danielbloy/pico-interactive-halloween/3d_models/fire/4xAA Battery Holder.png

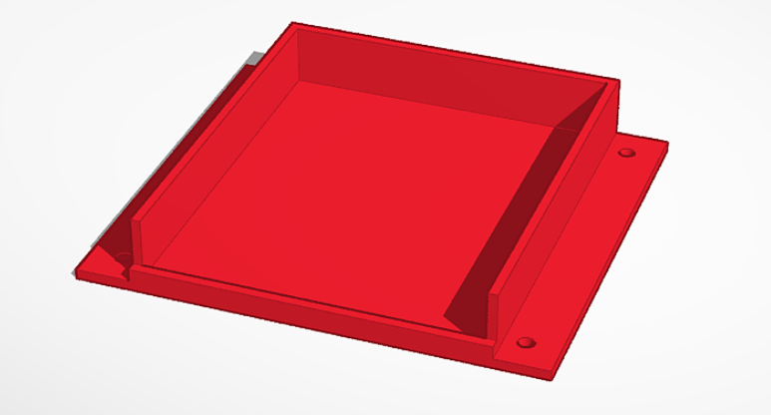
3d_models/fire/4xAA Battery Holder.png
