danielbloy/pico-interactive-halloween/3d_models/fire/Cable clip.png

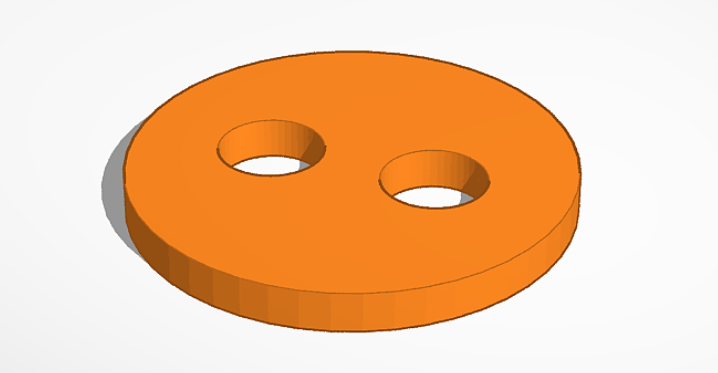
3d_models/fire/Cable clip.png
