danielbloy/pico-interactive-halloween/3d_models/fire/Circuit Board Holder.png

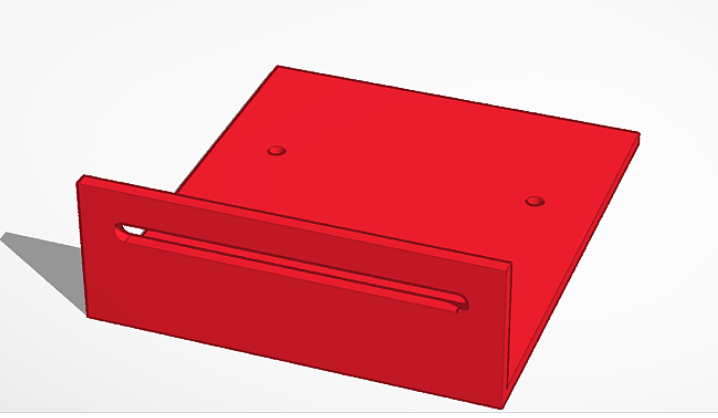
3d_models/fire/Circuit Board Holder.png
