danielbloy/pico-interactive-halloween/3d_models/fire/Eigth turn with holes.png

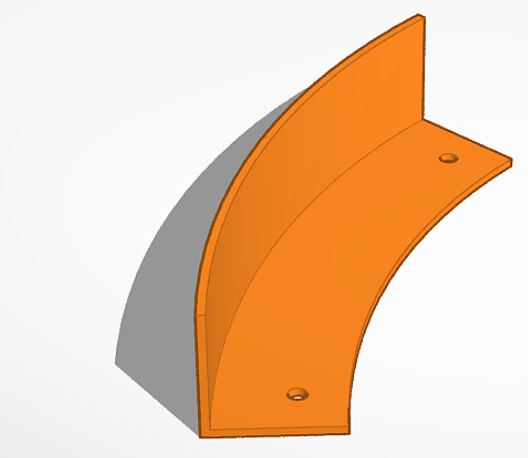
3d_models/fire/Eigth turn with holes.png
