danielbloy/pico-interactive-halloween/3d_models/fire/Eigth turn.png

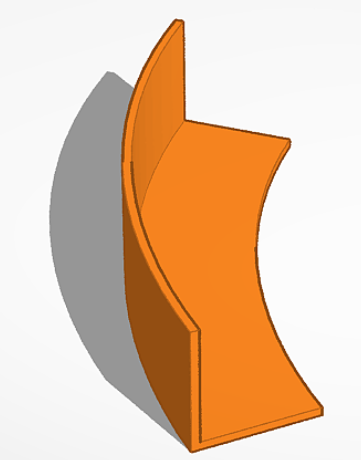
3d_models/fire/Eigth turn.png
