danielbloy/pico-interactive-halloween/3d_models/fire/Quater turn.png

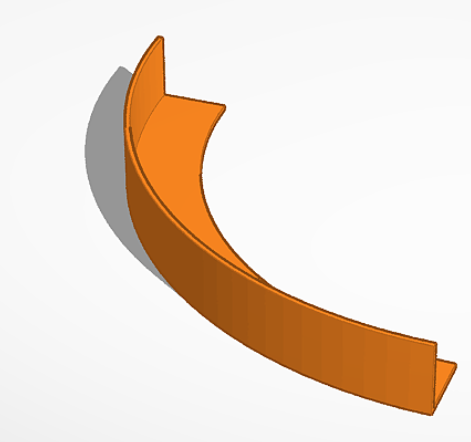
3d_models/fire/Quater turn.png
