danielbloy/pico-interactive-halloween/3d_models/speaker/Speaker Box Cover.stl

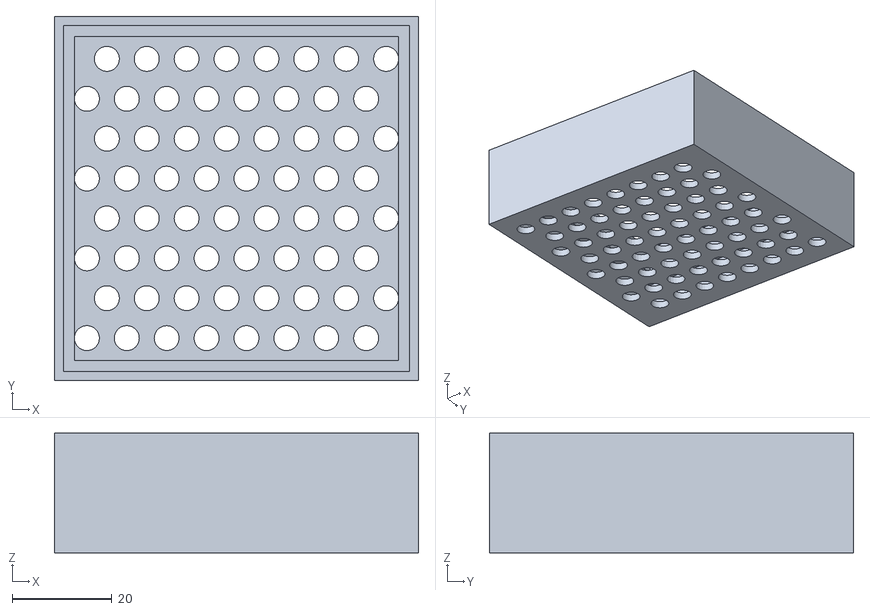
[picture p44: CAD file, 2024-10-30]
3d_models/speaker/Speaker Box Cover.stl
73.0 x 73.0 x 24.0
