danielbloy/pico-interactive-halloween/3d_models/spiders/Holder Mk 2.stl

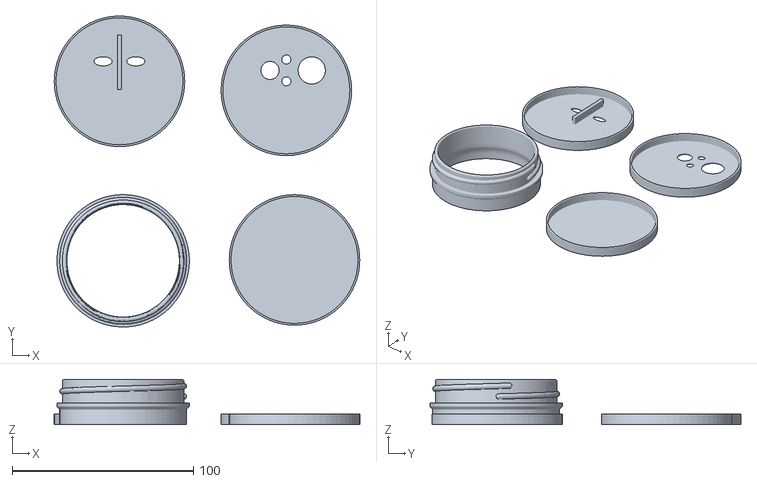
[picture p45: CAD file, 2024-10-30]
3d_models/spiders/Holder Mk 2.stl
168.5 x 171.5 x 25.0
