danielbloy/pico-interactive-halloween/3d_models/ultrasonic/Small Ultrasonic Clip.stl

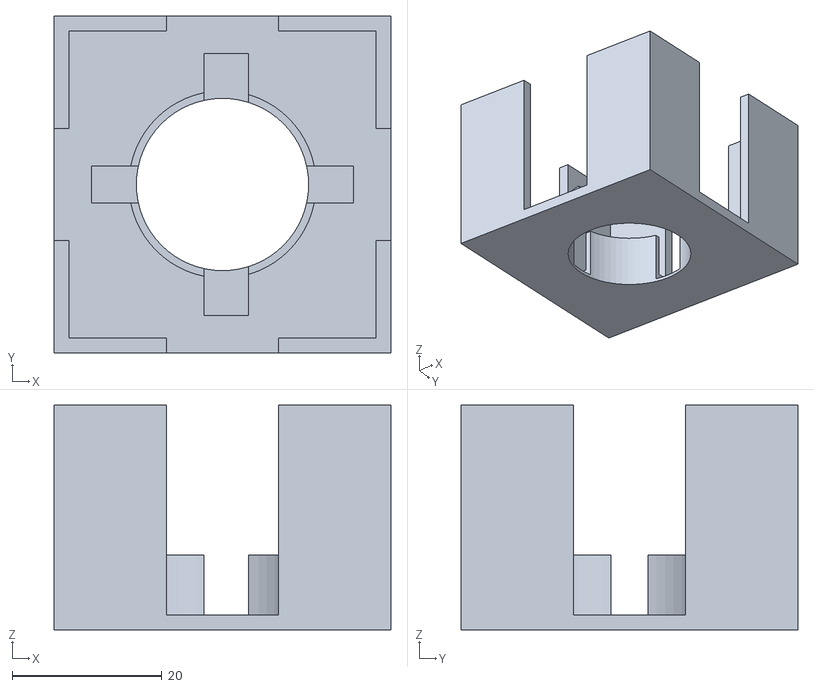
[picture p46: CAD file, 2024-10-30]
3d_models/ultrasonic/Small Ultrasonic Clip.stl
45.0 x 45.0 x 30.0
