danielbloy/pico-interactive-halloween/3d_models/fire/4xAA Battery Holder.stl

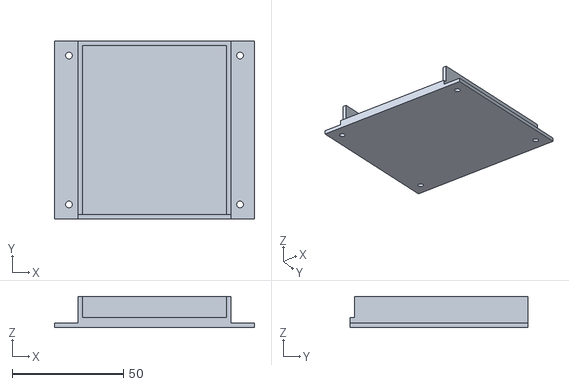
[picture p47: CAD file, 2025-09-02]
3d_models/fire/4xAA Battery Holder.stl
90.0 x 80.0 x 14.0
