danielbloy/pico-interactive-halloween/3d_models/skull_jar/Mason_jar_12mm_hole.stl

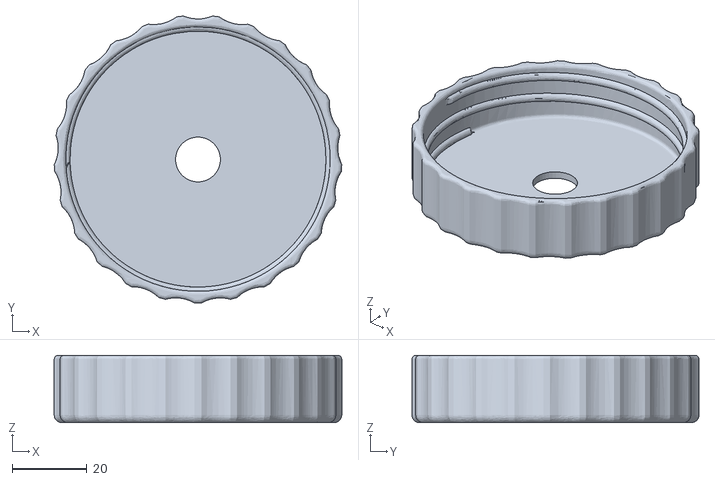
[picture p48: CAD file, 2024-10-30]
3d_models/skull_jar/Mason_jar_12mm_hole.stl
76.9 x 76.8 x 18.0
