danielbloy/pico-interactive-halloween/3d_models/spiders/Spider Pattern.stl

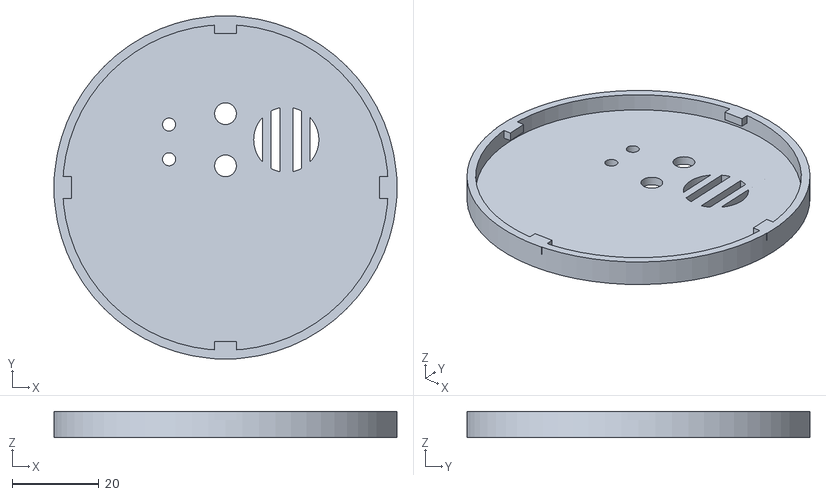
[picture p49: CAD file, 2024-10-30]
3d_models/spiders/Spider Pattern.stl
79.0 x 79.0 x 6.00
