danielbloy/pico-interactive-halloween/3d_models/ultrasonic/Ultrasonic Clip.stl

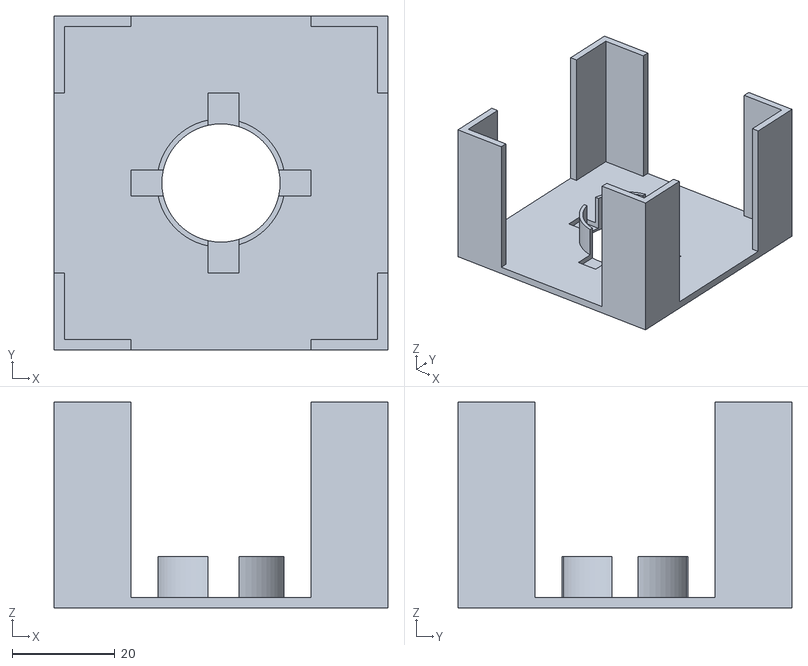
[picture p50: CAD file, 2024-10-30]
3d_models/ultrasonic/Ultrasonic Clip.stl
65.0 x 65.0 x 40.0
