danielbloy/pico-interactive-halloween/3d_models/fire/Cable clip.stl

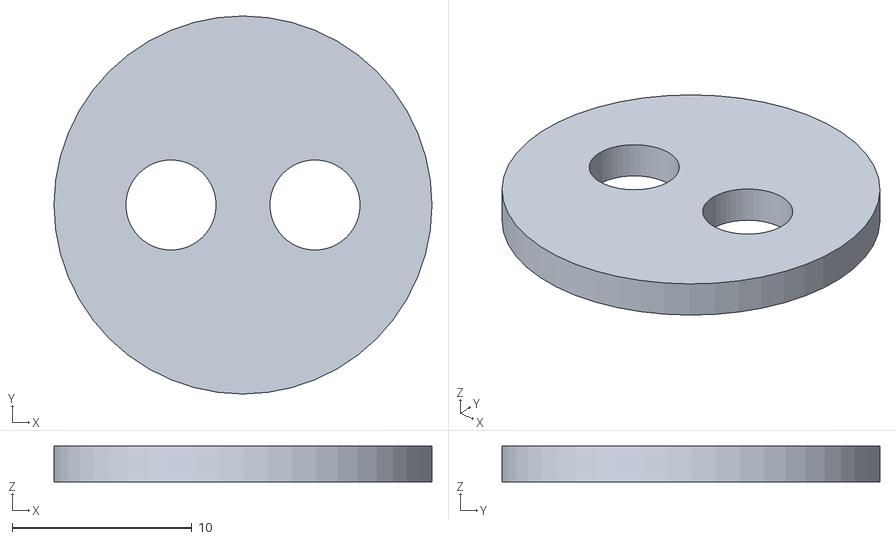
[picture p51: CAD file, 2025-09-02]
3d_models/fire/Cable clip.stl
21.0 x 21.0 x 2.00
