danielbloy/pico-interactive-halloween/3d_models/skull_jar/Neopixel_ring_holder_52mm_base.stl

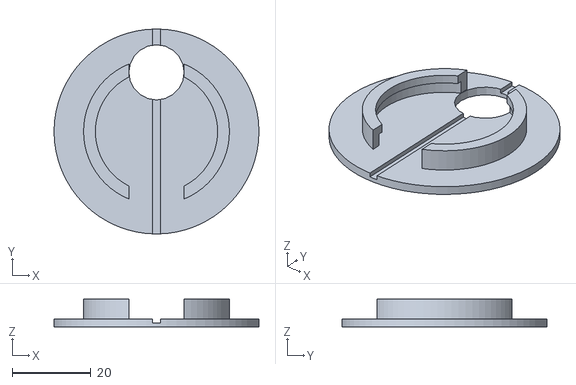
[picture p52: CAD file, 2024-10-30]
3d_models/skull_jar/Neopixel_ring_holder_52mm_base.stl
52.0 x 52.0 x 7.00
