danielbloy/pico-interactive-halloween/3d_models/spiders/Holder.stl

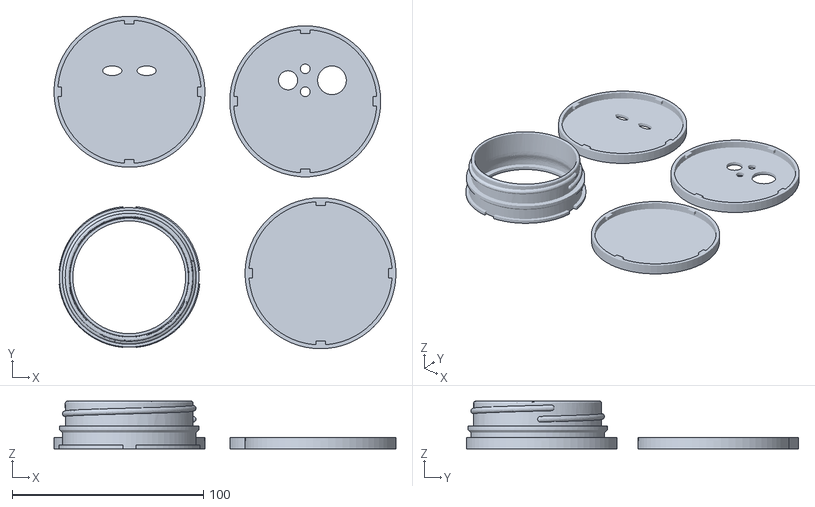
[picture p53: CAD file, 2024-10-30]
3d_models/spiders/Holder.stl
179.0 x 174.0 x 25.0
