danielbloy/pico-interactive-halloween/3d_models/ultrasonic/Ultrasonic Box Plugs.stl

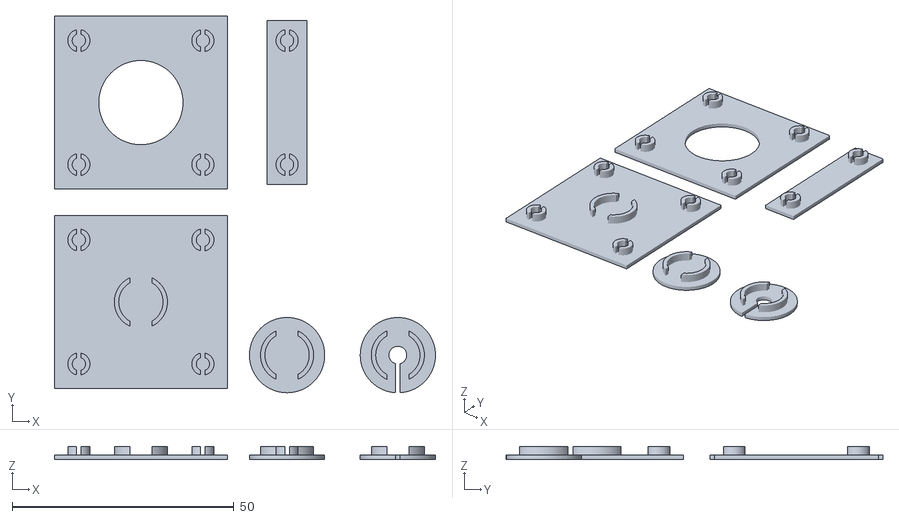
[picture p54: CAD file, 2024-10-30]
3d_models/ultrasonic/Ultrasonic Box Plugs.stl
86.0 x 85.0 x 3.00
