danielbloy/pico-interactive-halloween/3d_models/fire/Circuit Board Holder.stl

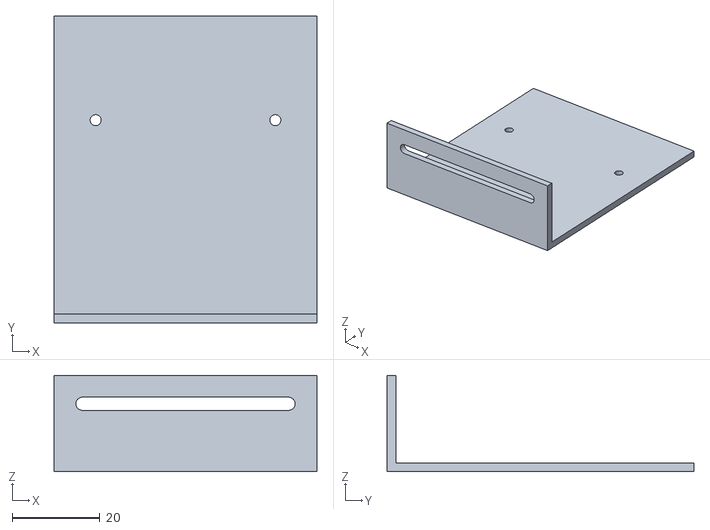
[picture p55: CAD file, 2025-09-02]
3d_models/fire/Circuit Board Holder.stl
60.0 x 70.0 x 22.0
