danielbloy/pico-interactive-halloween/3d_models/skull_jar/Neopixel_ring_holder_57mm_clip.stl

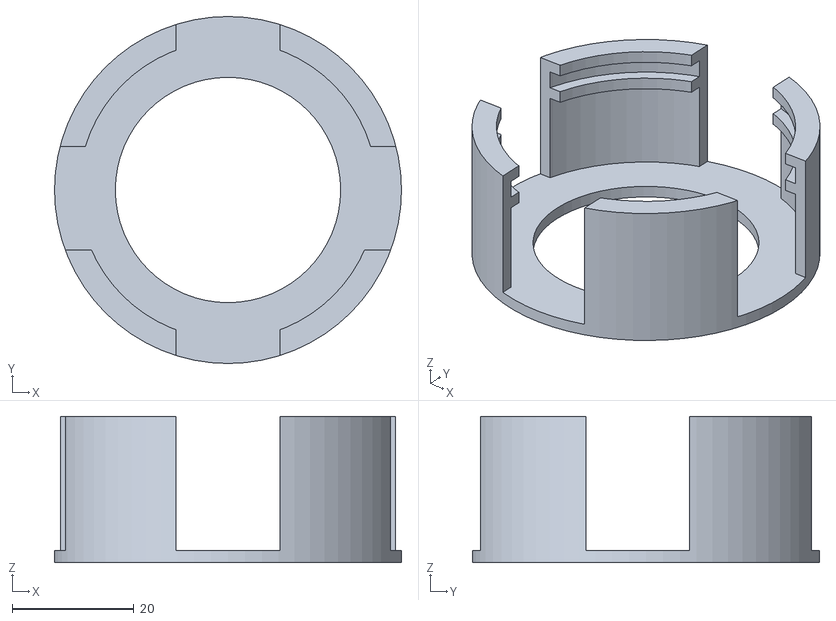
[picture p56: CAD file, 2024-10-30]
3d_models/skull_jar/Neopixel_ring_holder_57mm_clip.stl
57.0 x 57.0 x 24.0
