danielbloy/pico-interactive-halloween/3d_models/ultrasonic/Ultrasonic Box.stl

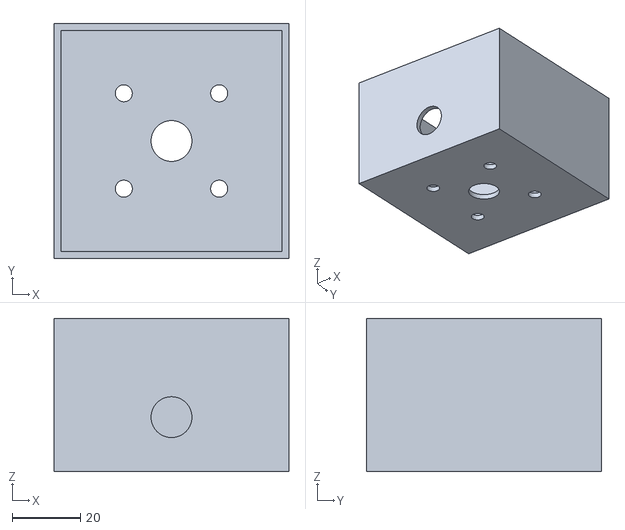
[picture p57: CAD file, 2024-10-30]
3d_models/ultrasonic/Ultrasonic Box.stl
69.0 x 69.0 x 45.0
