danielbloy/pico-interactive-halloween/3d_models/fire/Quater turn.stl

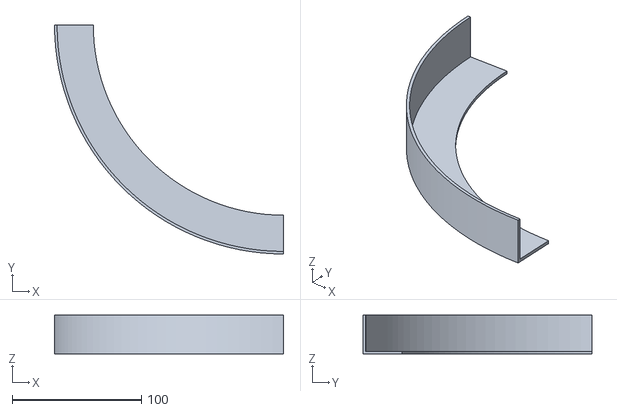
[picture p58: CAD file, 2025-09-02]
3d_models/fire/Quater turn.stl
177.0 x 177.0 x 30.0
