danielbloy/pico-interactive-halloween/3d_models/skull_jar/Mason_jar_id_with_57mm_clip.stl

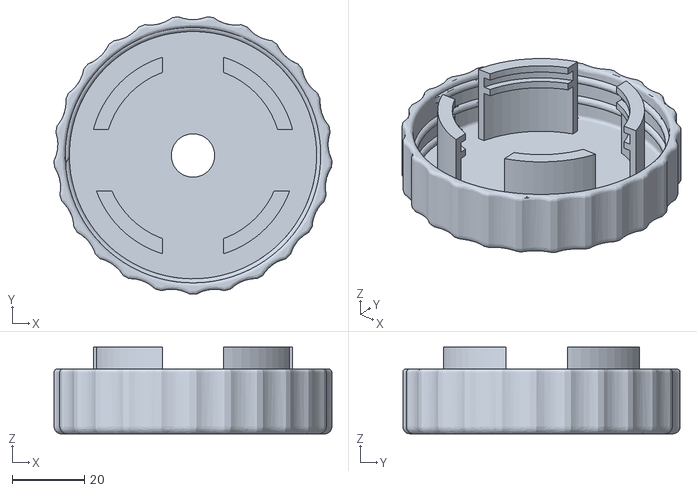
[picture p59: CAD file, 2024-10-30]
3d_models/skull_jar/Mason_jar_id_with_57mm_clip.stl
76.9 x 76.8 x 24.0
