danielbloy/pico-interactive-halloween/3d_models/skull_jar/Neopixel_ring_holder_52mm_base_tall.stl

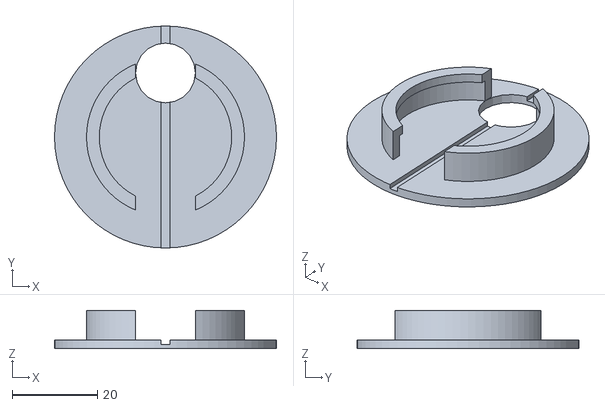
[picture p60: CAD file, 2024-10-30]
3d_models/skull_jar/Neopixel_ring_holder_52mm_base_tall.stl
52.0 x 52.0 x 9.00
