danielbloy/pico-interactive-halloween/microcontroller/makecode-arcade/eyes/arcade-eye-animation-blink-red-modified-ultrassonic.png

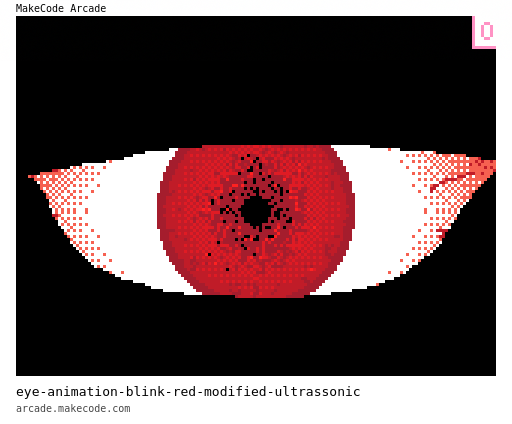
microcontroller/makecode-arcade/eyes/arcade-eye-animation-blink-red-modified-ultrassonic.png
