danielbloy/pico-interactive-halloween/microcontroller/makecode-arcade/eyes/constructing_new_eyes/1_original_creepy_head_box.jpg

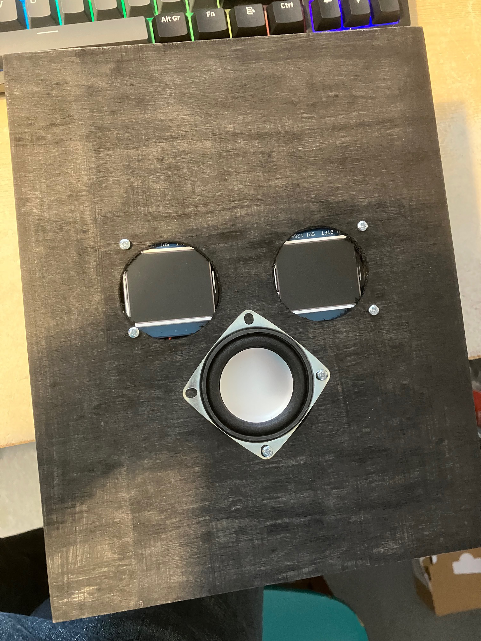
microcontroller/makecode-arcade/eyes/constructing_new_eyes/1_original_creepy_head_box.jpg
