danielbloy/pico-interactive-halloween/microcontroller/makecode-arcade/eyes/constructing_new_eyes/1b_original_creepy_head_inside.jpg

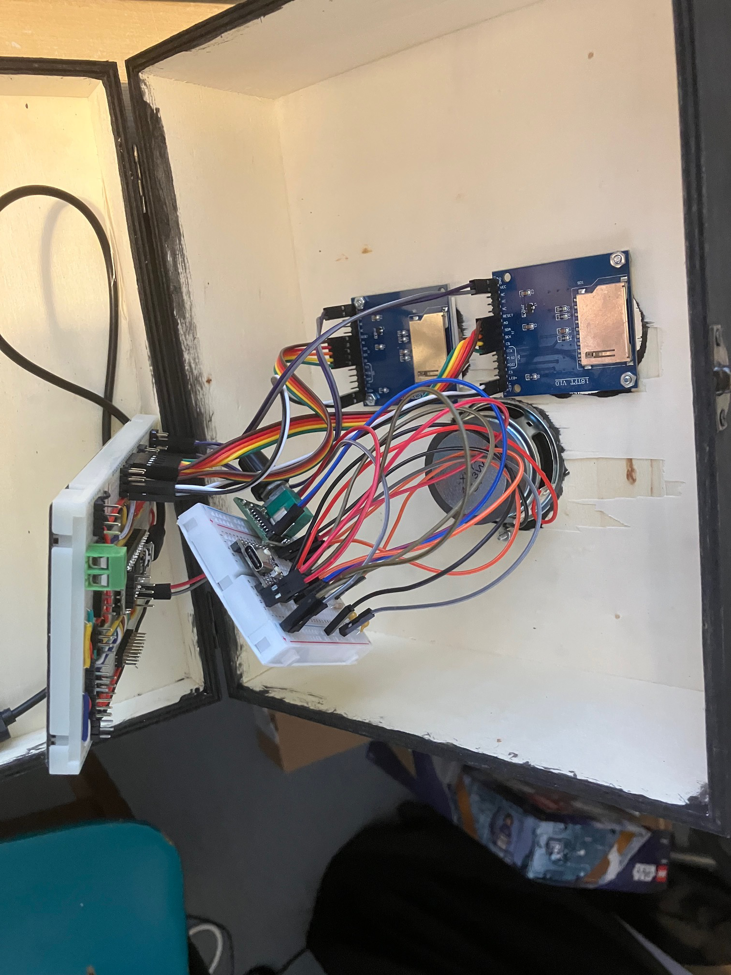
microcontroller/makecode-arcade/eyes/constructing_new_eyes/1b_original_creepy_head_inside.jpg
