danielbloy/pico-interactive-halloween/microcontroller/makecode-arcade/eyes/constructing_new_eyes/2b_original_creepby_head_insides_removed.jpg

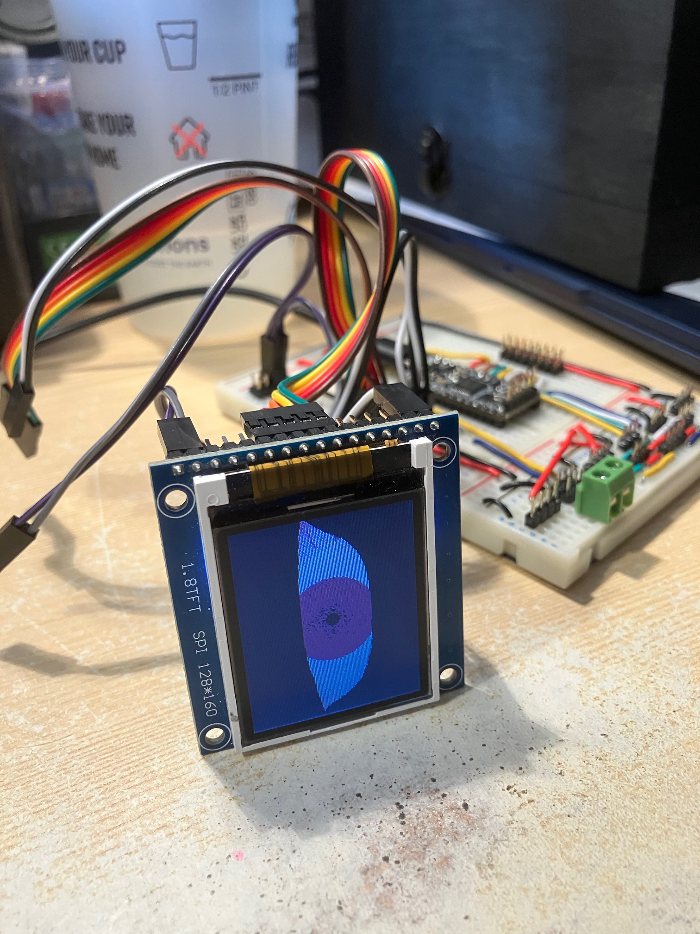
microcontroller/makecode-arcade/eyes/constructing_new_eyes/2b_original_creepby_head_insides_removed.jpg
