danielbloy/pico-interactive-halloween/microcontroller/makecode-arcade/eyes/constructing_new_eyes/3a_new_3D_printed_screen_mount.jpg

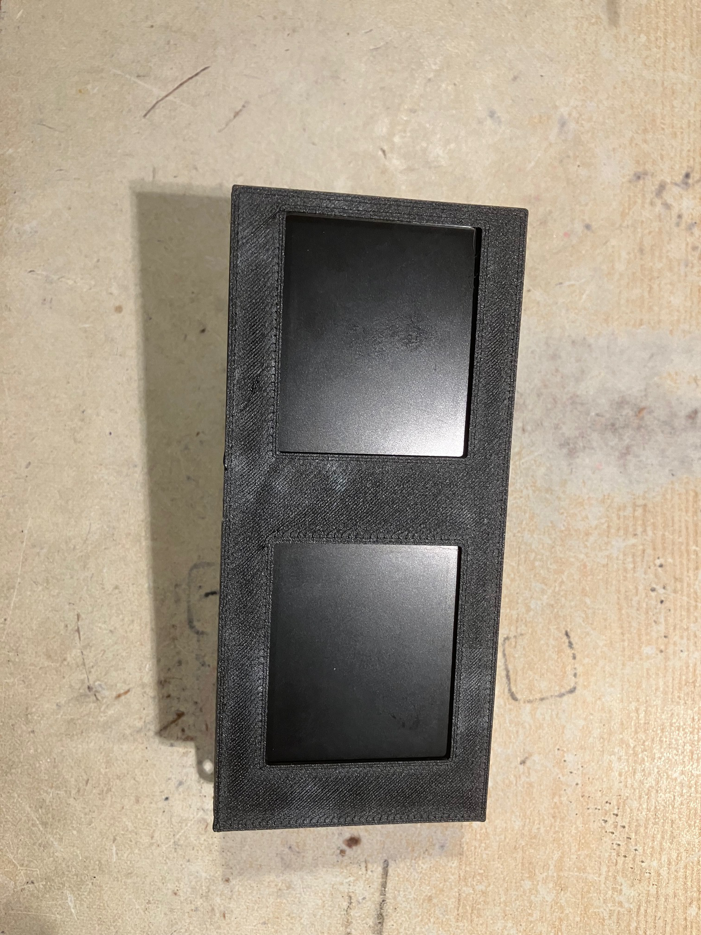
microcontroller/makecode-arcade/eyes/constructing_new_eyes/3a_new_3D_printed_screen_mount.jpg
