danielbloy/pico-interactive-halloween/microcontroller/makecode-arcade/eyes/constructing_new_eyes/3b_new_3D_printed_screen_mount.jpg

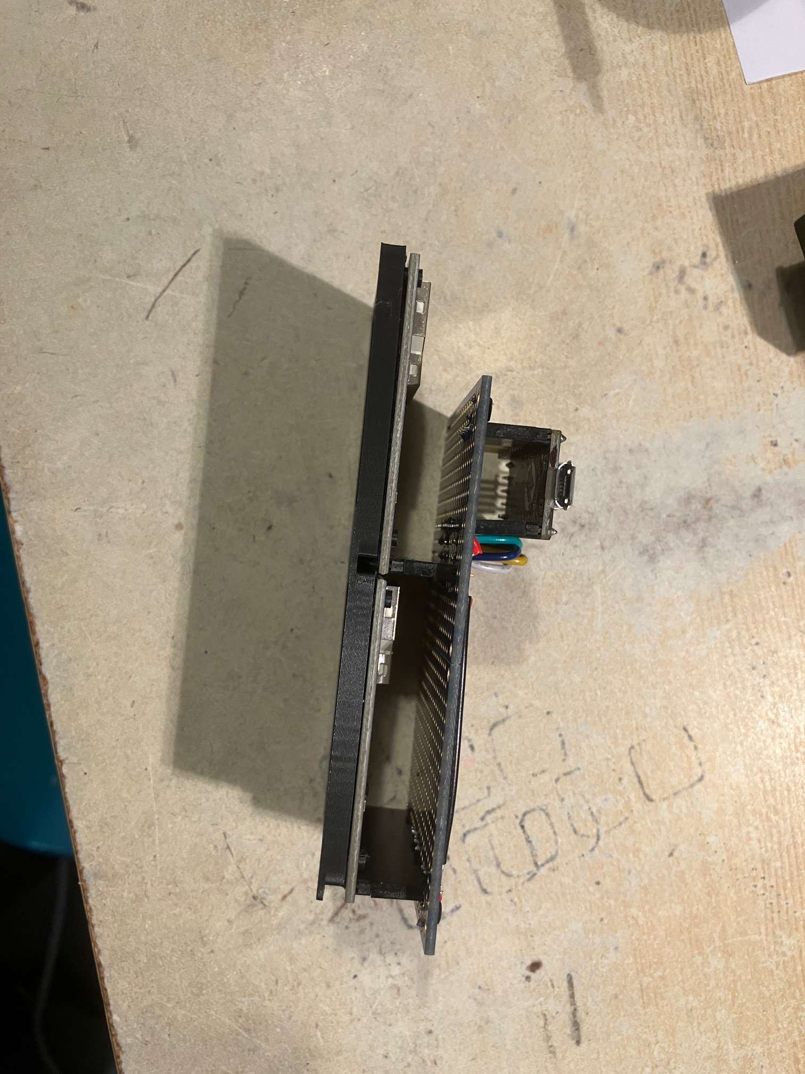
microcontroller/makecode-arcade/eyes/constructing_new_eyes/3b_new_3D_printed_screen_mount.jpg
