danielbloy/pico-interactive-halloween/microcontroller/makecode-arcade/eyes/constructing_new_eyes/5a_new_eyes_running.jpg

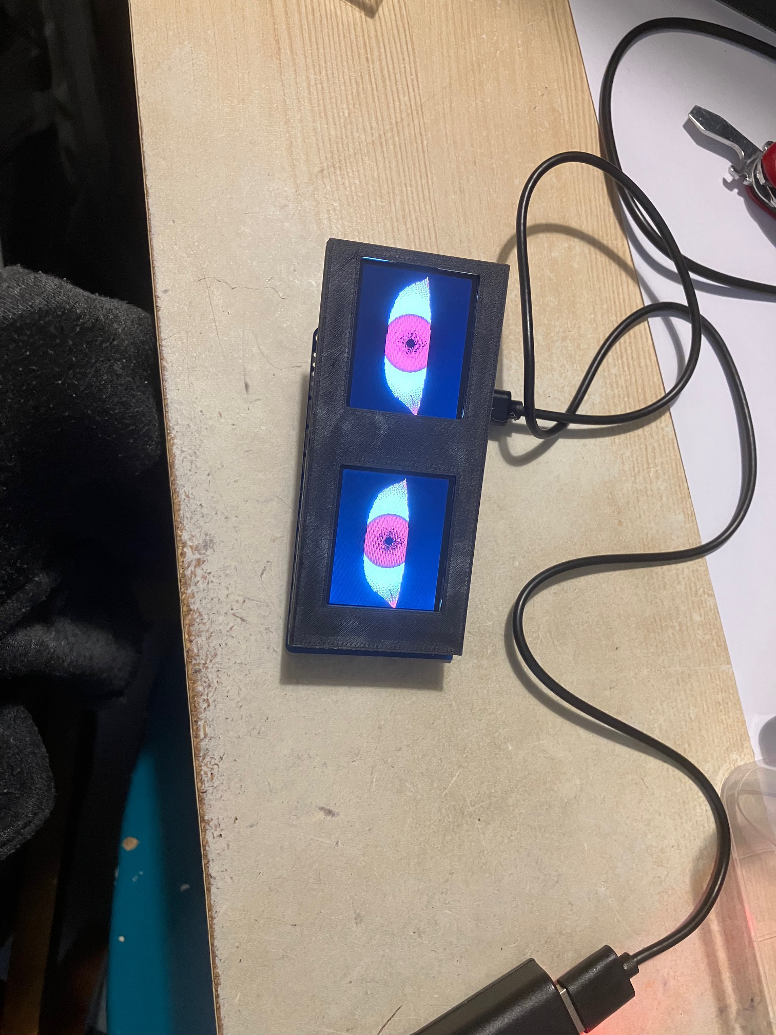
microcontroller/makecode-arcade/eyes/constructing_new_eyes/5a_new_eyes_running.jpg
