danielbloy/pico-interactive-halloween/microcontroller/makecode-arcade/eyes/original/arcade-eye-animation-blink-red-eyes.png

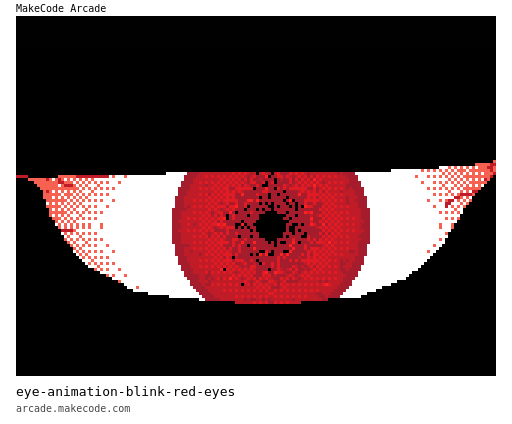
microcontroller/makecode-arcade/eyes/original/arcade-eye-animation-blink-red-eyes.png
