danielbloy/pico-interactive-halloween/microcontroller/pico-interactive/graveyard/graveyard_config.py

# NOTE: Rename this to config.py on the graveyard node microcontroller.
# This code runs on a Pimoroni Tiny 2040
import board

from interactive.polyfills.animation import RED, ORANGE, AMBER, BLUE, GREEN, YELLOW, WHITE

BUTTON_PIN = board.GP4
AUDIO_PIN = board.GP26

SPIDER_PINS = [board.GP0, board.GP1, board.GP2, board.GP5, board.GP6, board.GP7]
SPIDER_PIXELS = 4
SPIDER_COLOURS = [RED, ORANGE, AMBER, BLUE, GREEN, YELLOW]
SPIDER_PERIODS = [3, 2, 4, 1, 5, 2]
SPIDER_BRIGHTNESS = 0.5
SPIDER_SPEED = 0.1 

LIGHTNING_PIN = board.GP3
LIGHTNING_PIXELS = 24
LIGHTNING_COLOUR = WHITE
LIGHTNING_MIN_FLASHES = 5
LIGHTNING_MAX_FLASHES = 15
LIGHTNING_MIN_BRIGHTNESS = 0.1
LIGHTNING_MAX_BRIGHTNESS = 1.0

TRIGGER_PIN = board.GP29
TRIGGER_DURATION = 40

REPORT_RAM = False
REPORT_RAM_PERIOD = 10

from interactive.log import CRITICAL

LOG_LEVEL = CRITICAL
