danielbloy/pico-interactive-halloween/microcontroller/pico-interactive/cauldron/config.py

# This code runs on a standard Pico 2W, using the 2026 Mark 3 node.
import board

from interactive.polyfills.animation import GREEN

AUDIO_PIN = board.GP26

CAULDRON_PIN = board.GP28
CAULDRON_COLOUR = GREEN
CAULDRON_BRIGHTNESS = 1.0
CAULDRON_SPEED = 0.03

TRIGGER_PIN = board.GP9
TRIGGER_DURATION = 40

REPORT_RAM = False
REPORT_RAM_PERIOD = 10

from interactive.log import CRITICAL

LOG_LEVEL = CRITICAL
